Terminal-Curiosity/NixieClock/docs/Datasheets/IN-16 Footprint coordinates.PNG

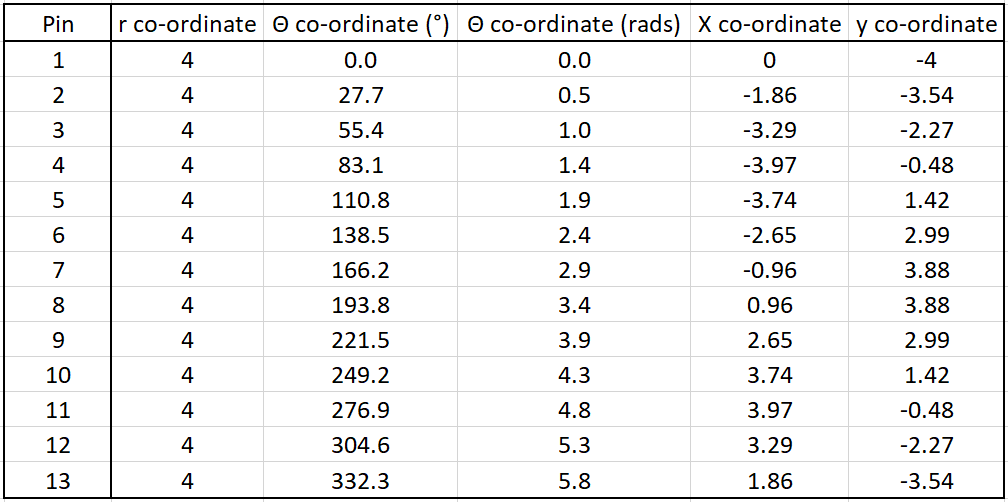
docs/Datasheets/IN-16 Footprint coordinates.PNG
