Terminal-Curiosity/NixieClock/docs/Datasheets/IN-16 Footprint only.PNG

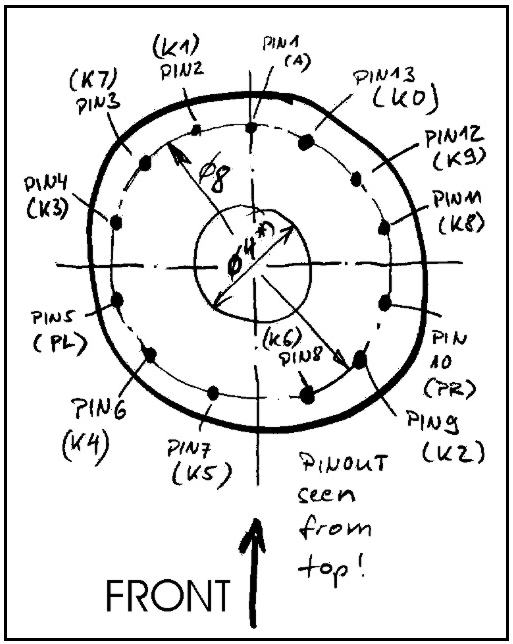
docs/Datasheets/IN-16 Footprint only.PNG
