Terminal-Curiosity/NixieClock/docs/Datasheets/table with diameter highlighted.png

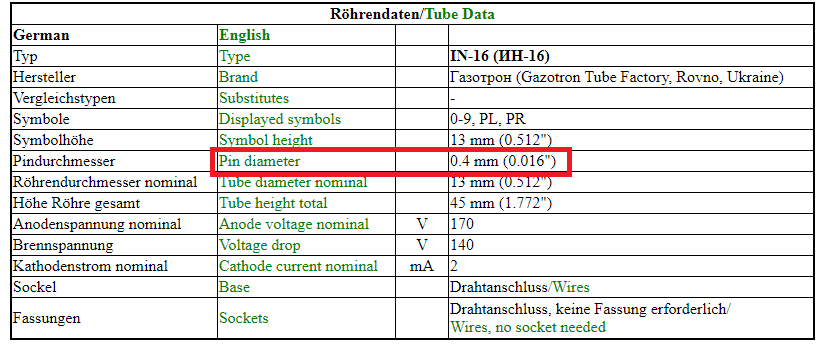
docs/Datasheets/table with diameter highlighted.png
