Terminal-Curiosity/NixieClock/docs/images/20250507_163642.jpg

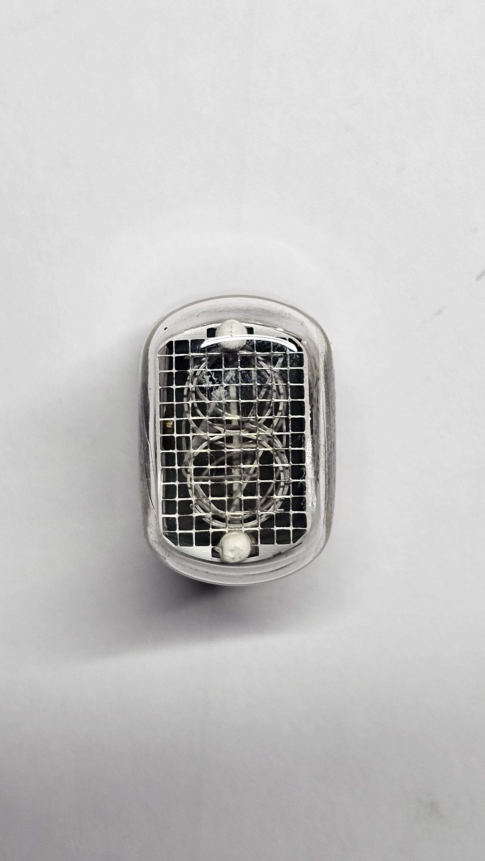
docs/images/20250507_163642.jpg
