Terminal-Curiosity/NixieClock/docs/images/tube image.png

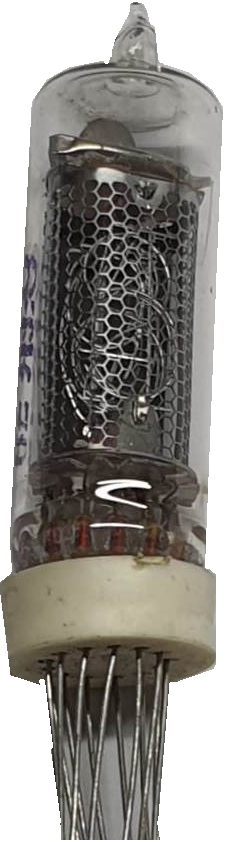
docs/images/tube image.png
